mulcmu/Plimsoll/alpha_test/loadgraph_freq.png

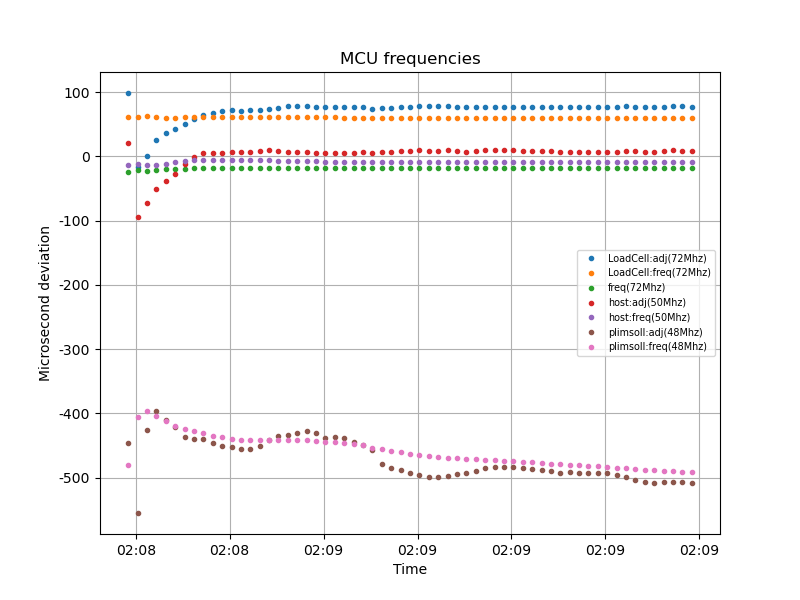
alpha_test/loadgraph_freq.png
