mulcmu/Plimsoll/alpha_test/plimsoll r0 (Custom).jpg

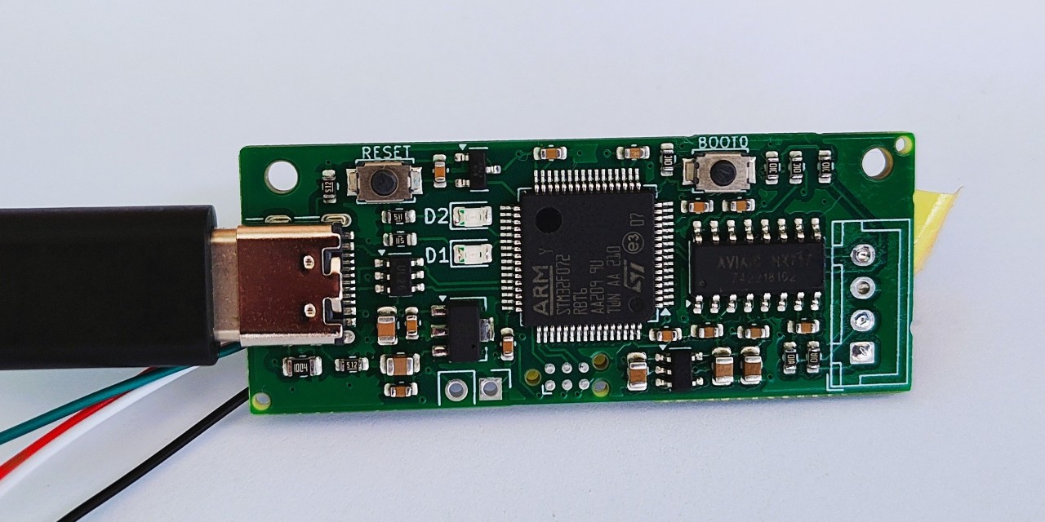
alpha_test/plimsoll r0 (Custom).jpg
