mulcmu/Plimsoll/alpha_test/plimsoll.png

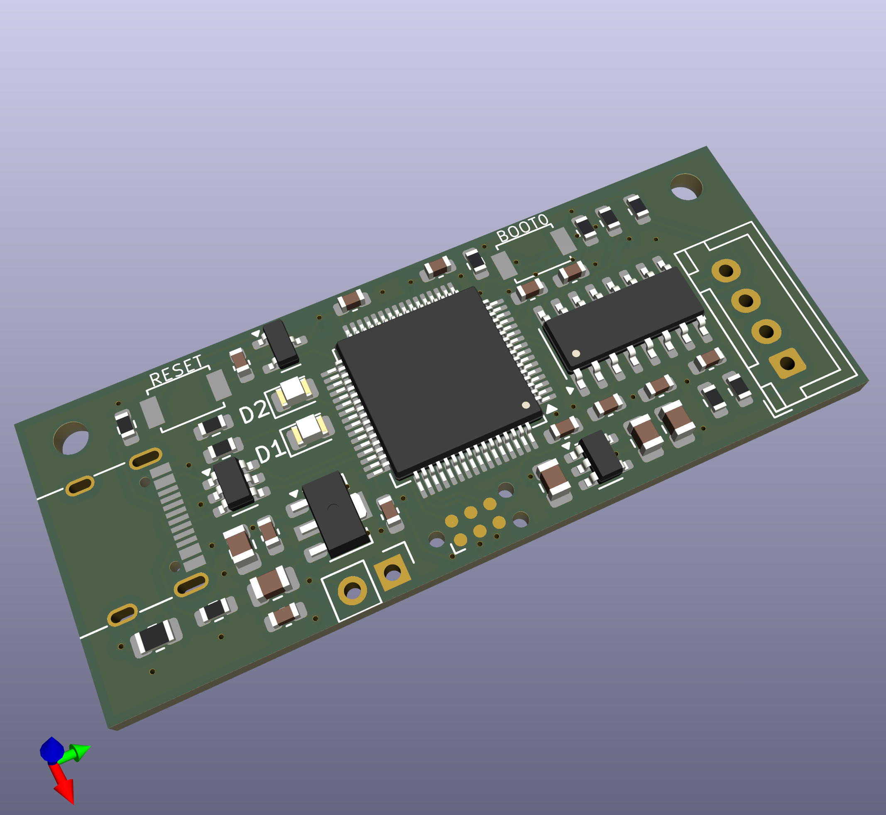
alpha_test/plimsoll.png
